ARTSAT/INVADER/satellite/body/hardware/Inventor/FM_ver3_1/Invader_cam_cad_rev2.pdf

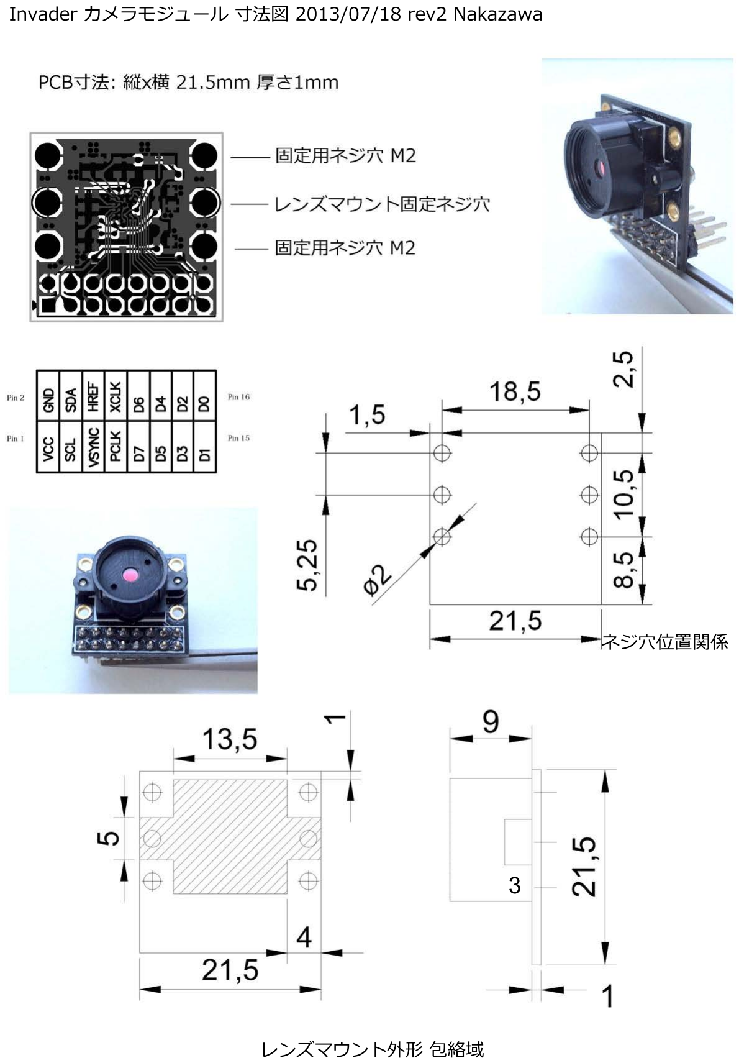
[picture p3: page 1]

ネジ穴位置関係

3

Invader カメラモジュール 寸法図 2013/07/18 rev2 Nakazaw a

レンズマウント外形 包絡域
