ARTSAT/INVADER/satellite/body/hardware/Inventor/FM_ver3_1/body_ver3.17.pdf

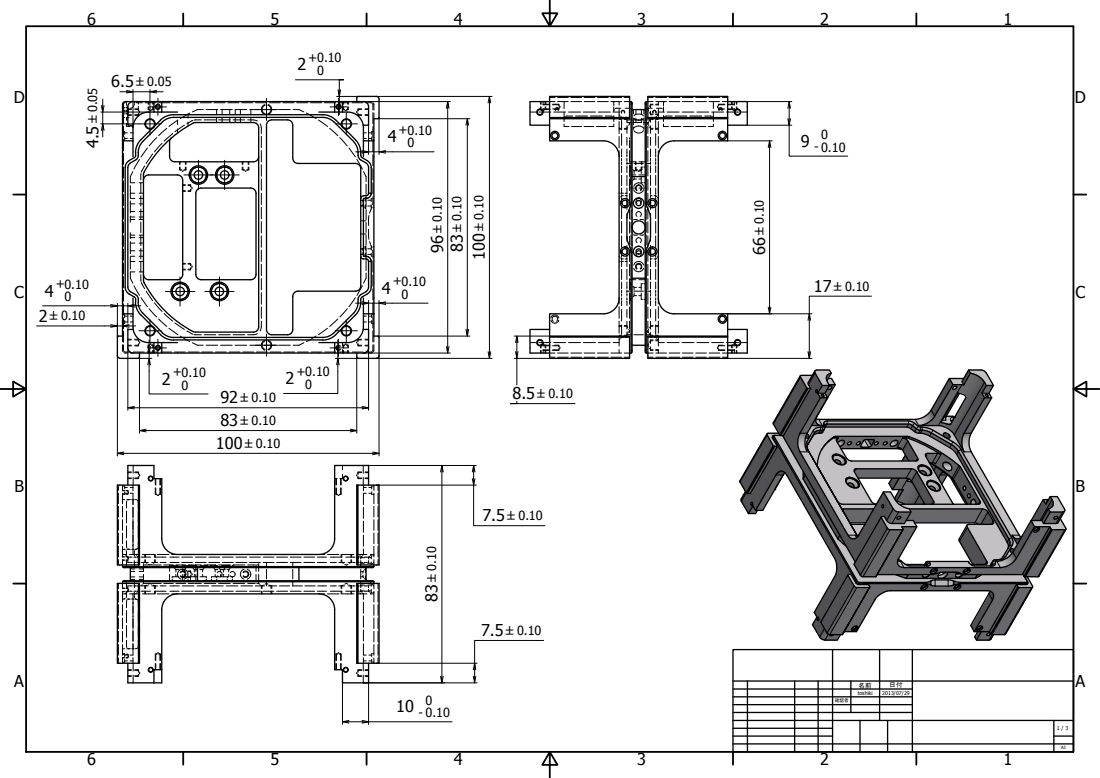
[picture p55: page 1]

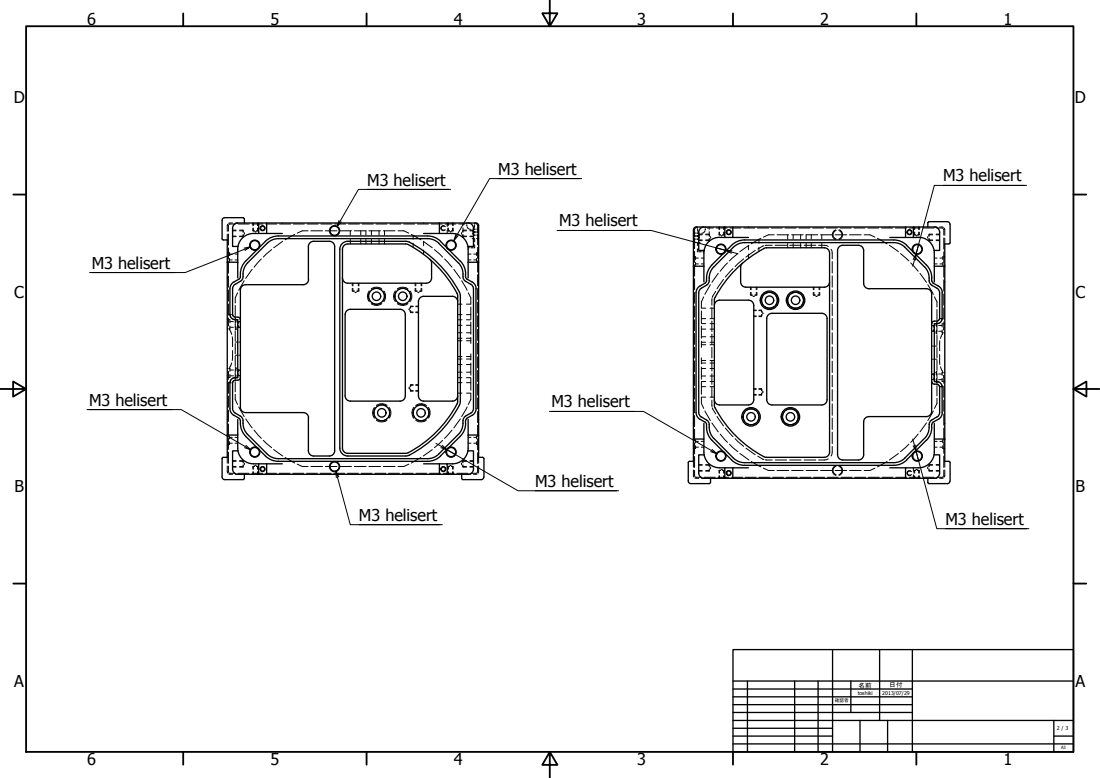
[picture p56: page 2]
M3 helisert

toshiki | 2013/07/29

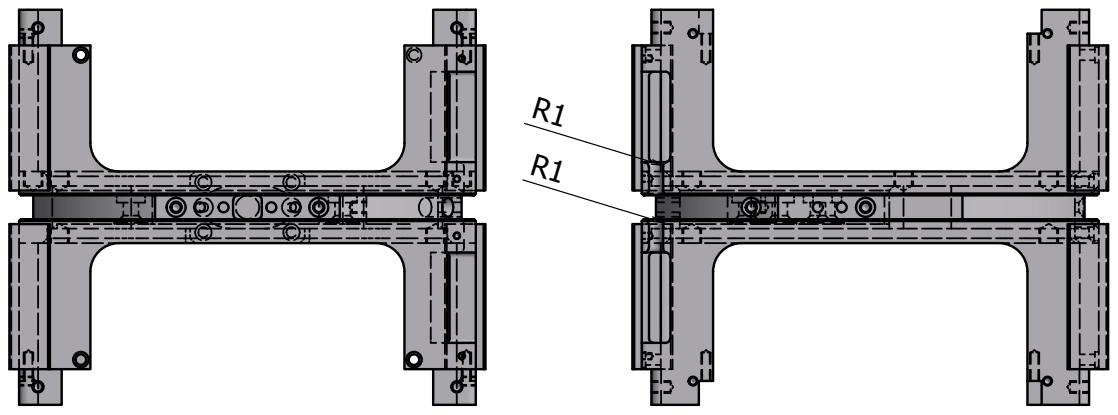
[picture p57: page 3]
