ARTSAT/INVADER/satellite/mission/hardware/EAGLE/OV_CAM/OV_CAM_brd.pdf

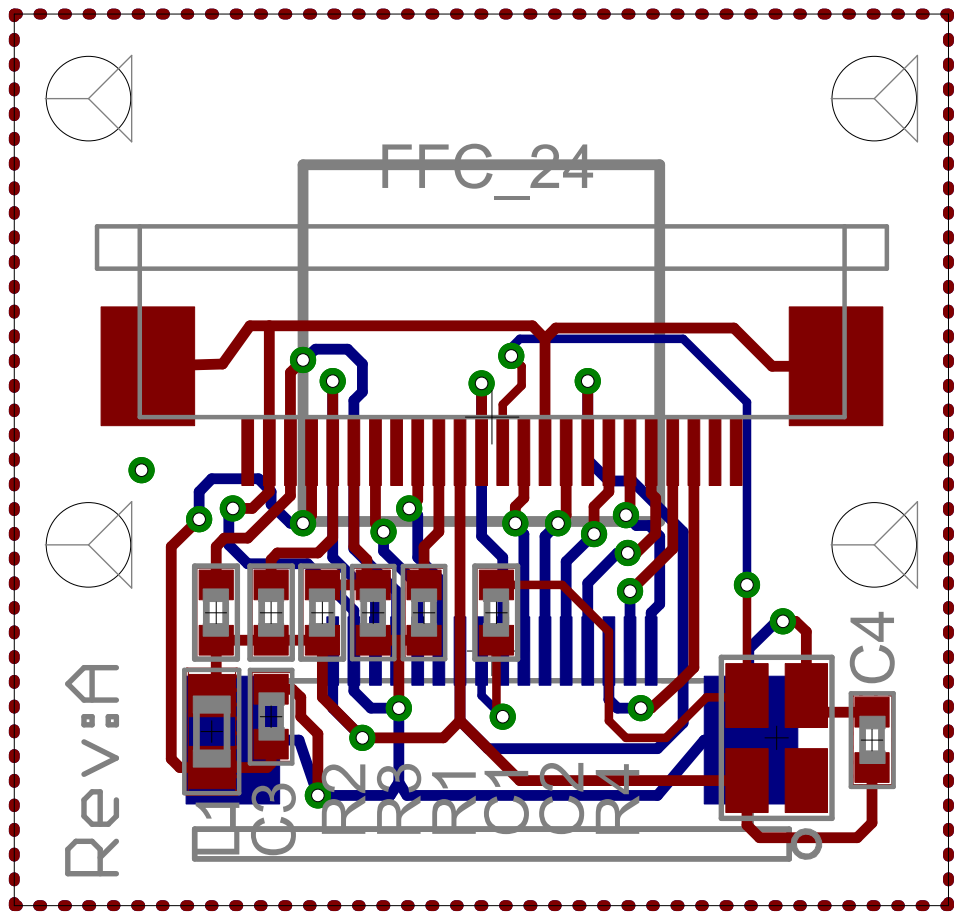
[picture p58: page 1]
