ARTSAT/INVADER/satellite/mission/hardware/EAGLE/OV_CAM/OV_CAM_sch.pdf

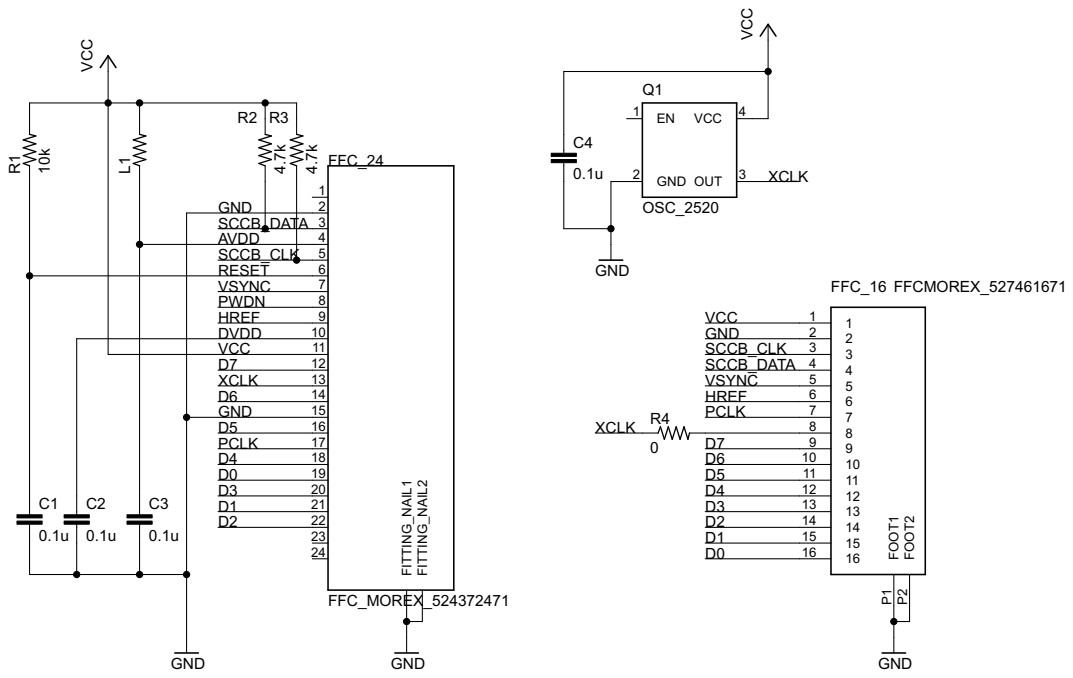
[picture p59: page 1]
