ARTSAT/INVADER/satellite/mission/hardware/EAGLE/OV_FPC/OV_FPC_brd.pdf

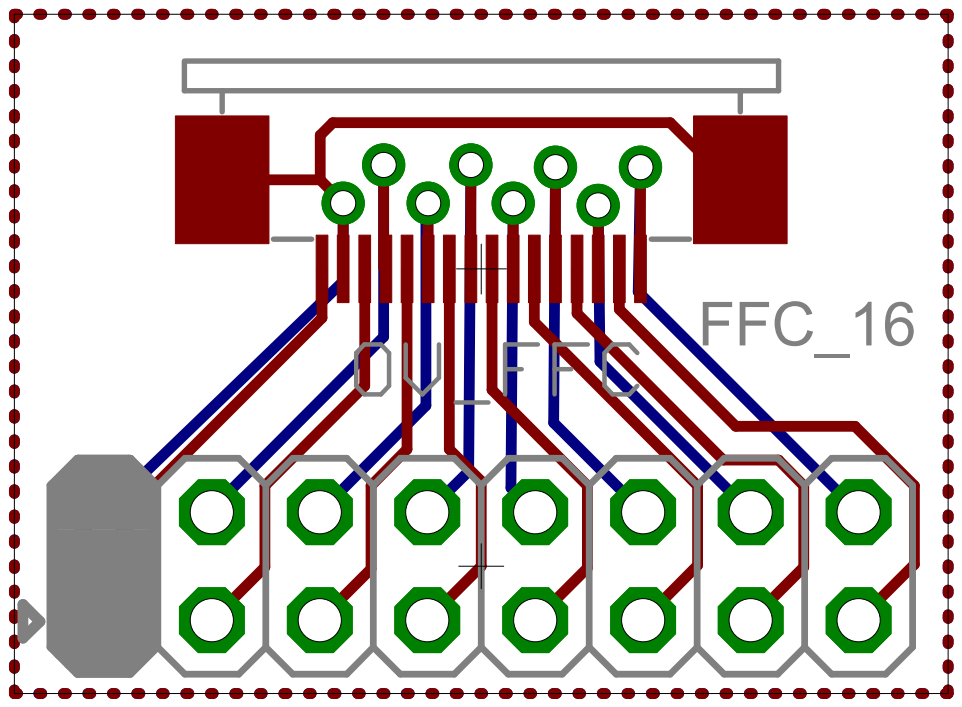
[picture p60: page 1]
