ARTSAT/INVADER/satellite/mission/hardware/EAGLE/OV_FPC/OV_FPC_sch.pdf

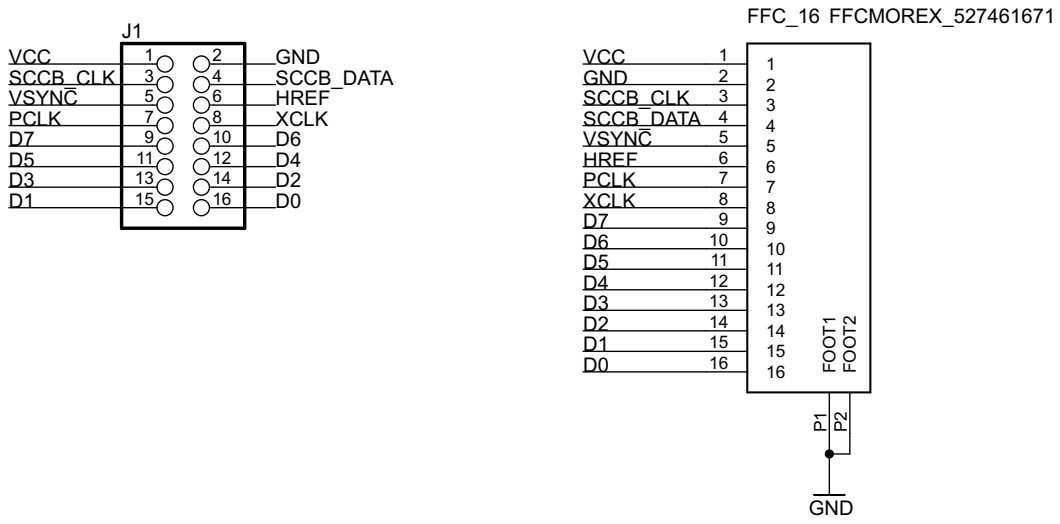
[picture p61: page 1]
