ARTSAT/INVADER/satellite/main/software/HEW/H8_software/20120510/global.c

/******************************************************************************
* ファイル名　：　global.c
* タイトル　　：　INVADER用グローバル変数関連プログラム
* 製作者　　　：　03-110317 木村元紀
* 所属　　　　：　東京大学工学部航空宇宙工学科
* 製作日　　　：　2012.1.30
* 言語　　　　：　C
*******************************************************************************
* ※備考※
*
******************************************************************************/
#include "iodefine.h"
#include "global.h"

#include "message.h"
#include "pwr.h"
#include "mission.h"
#include "adconv.h"
#include "teleme.h"
#include "itu1.h"

/*************************************************
		ステータス情報初期化関数
*************************************************/
unsigned char InitStatus(void)
{
	unsigned char i;
	
	for(i=0;i<SIZE_OBCTIME;i++)		status.obctime[i] = 0x00;
  
	for(i=0;i<SIZE_VOLTAGE;i++)		status.voltage[i] = 0x00;
	
	for(i=0;i<SIZE_AMPARE;i++)		status.ampare[i] = 0x00;
	
	for(i=0;i<SIZE_TEMPERATURE;i++)	status.temperature[i] = 0x00;
	
	for(i=0;i<SIZE_GYRO;i++)		status.gyro[i] = 0x00;
	
	for(i=0;i<SIZE_MAGNET;i++)		status.magnet[i] = 0x00;
	
	for(i=0;i<SIZE_RSSI;i++)		status.rssi[i] = 0x00;
  
	for(i=0;i<SIZE_MISSION;i++)		status.mission[i] = 0x00;
	
	for(i=0;i<SIZE_POWER;i++)		status.power[i] = 0x00;
	
	for(i=0;i<SIZE_INIT;i++)		status.init[i] = 0x00;
	
	for(i=0;i<SIZE_MODE;i++)		status.mode[i] = 0x00;
	
	for(i=0;i<SIZE_CHARGEFLAG;i++)		status.chargeflag[i] = 0x00;
	
	for(i=0;i<SIZE_FLAG;i++)		status.flag[i] = 0x00;
	
	for(i=0;i<SIZE_ERROR;i++)		status.error_counter[i] = 0x00;
	
	for(i=0;i<SIZE_MESSAGE;i++)		status.message_counter[i] = 0x00;
	
	return 1;
}

/*************************************************
		ルーチン初期化関数
*************************************************/
unsigned char InitRoutine(void)
{
	/*
	1.Power Telemetry Request	: EN
	2.Mission Telemetry Send	: EN
	3.AD Convert				: EN
	4.Rough Telemetry			: EN
	5.Detail telemetry			: DIS
	6.API Telemetry				: EN
	7.My WDT					: DIS
	8.Over Ampare				: EN
	9.Initial Telemetry			: EN
	10.Alive					: EN
	11.DispAD					: DIS
	12.Output Telemetry			: EN
	*/

	SetFlags(ena_pwrt);
	SetFlags(ena_misst);
	SetFlags(ena_ad);
	SetFlags(ena_rteleme);
	ClearFlags(ena_dteleme);
	SetFlags(ena_ateleme);
	ClearFlags(ena_mywdt);
	SetFlags(ena_overa);
	SetFlags(ena_iteleme);
	SetFlags(ena_alive);
	ClearFlags(ena_dispAD);
	SetFlags(ena_oteleme);
	
	return 1;
}

/*************************************************
		フラグ多数決関数
*************************************************/
unsigned char CheckFlags(volatile unsigned char *f)
{
	unsigned char flag = 0;
	unsigned char flag_sum = 0;
	unsigned char i;
	
	for(i=0; i<3; i++){
		f[i] &= 0x01;		// マスク
		flag_sum += f[i];
	}
	
	if(flag_sum >= 2)	flag = 1;
	
	return flag;
}

/**************************************************
		フラグクリア関数
**************************************************/
void ClearFlags(volatile unsigned char *f)
{
	unsigned char i;
	
	for(i=0;i<3;i++){
		f[i] = 0x00;	
	}
}

/**************************************************
		フラグセット関数
**************************************************/
void SetFlags(volatile unsigned char *f)
{
	unsigned char i;
	
	for(i=0;i<3;i++){
		f[i] = 0x01;
	}
}
